impromptu1583/klipperSidekick/e_m175.cfg

[extruder]
step_pin: PC3
dir_pin: PL6
enable_pin: !PA4
microsteps: 16
rotation_distance: 7.7
nozzle_diameter: 0.400
filament_diameter: 1.750
heater_pin: PE5
#The Extruder uses 100K thermistor - CC-AO-E-SEMITEC-50-MOLEX
sensor_type: ATC Semitec 104NT-4-R025H42G
sensor_pin: PF0
control: pid
#pid_Kp: 21.358
#pid_Ki: 1.306
#pid_Kd: 87.303

# target 260
pid_Kp: 18.893
pid_Ki: 1.223
pid_Kd: 72.973


min_extrude_temp:160
min_temp: 0
max_temp: 280
max_extrude_cross_section: 20
max_extrude_only_distance: 200.0
pressure_advance=0.0325
